marsairforce/nobsound/pictures/IMG_5804.jpg

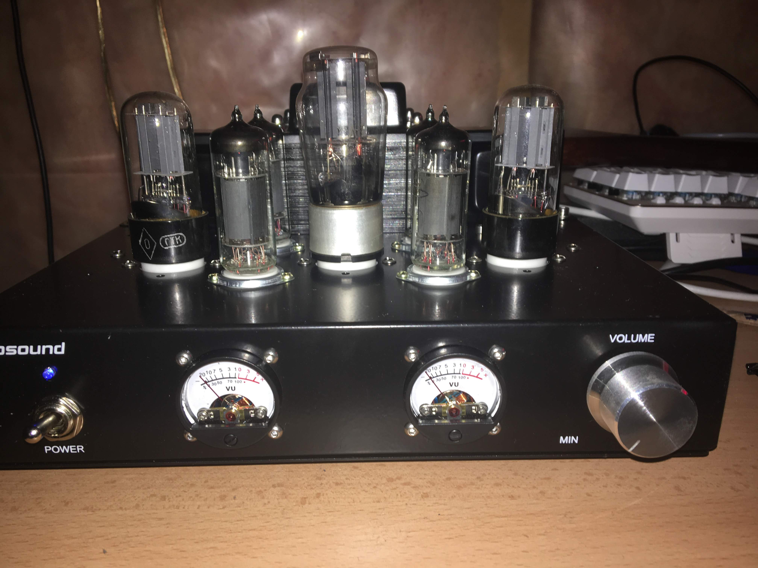
pictures/IMG_5804.jpg
