marsairforce/nobsound/pictures/IMG_5805.jpg

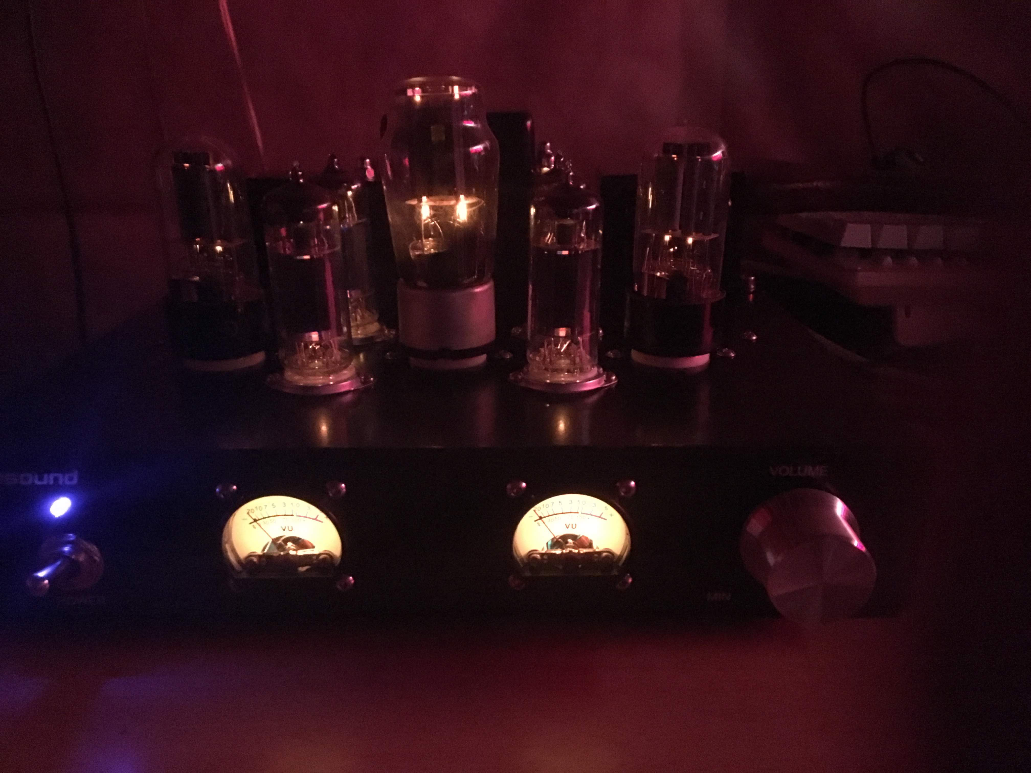
pictures/IMG_5805.jpg
