marsairforce/nobsound/pictures/IMG_9100.jpg

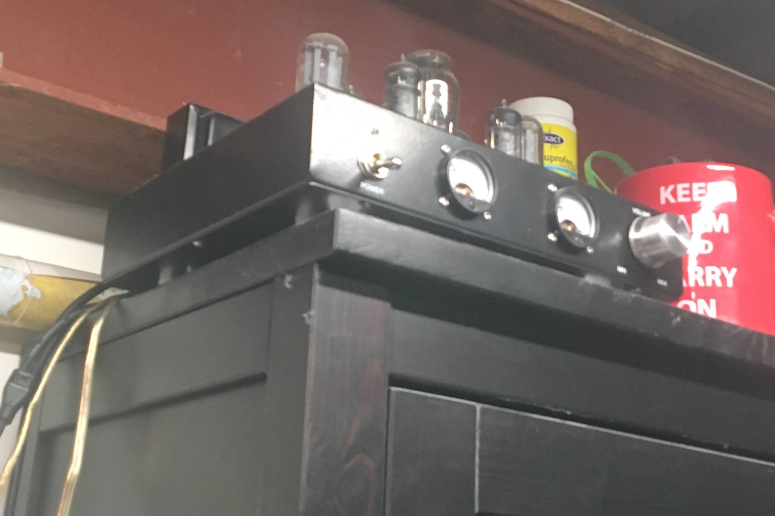
pictures/IMG_9100.jpg
