marsairforce/nobsound/pictures/IMG_9361(1).jpg

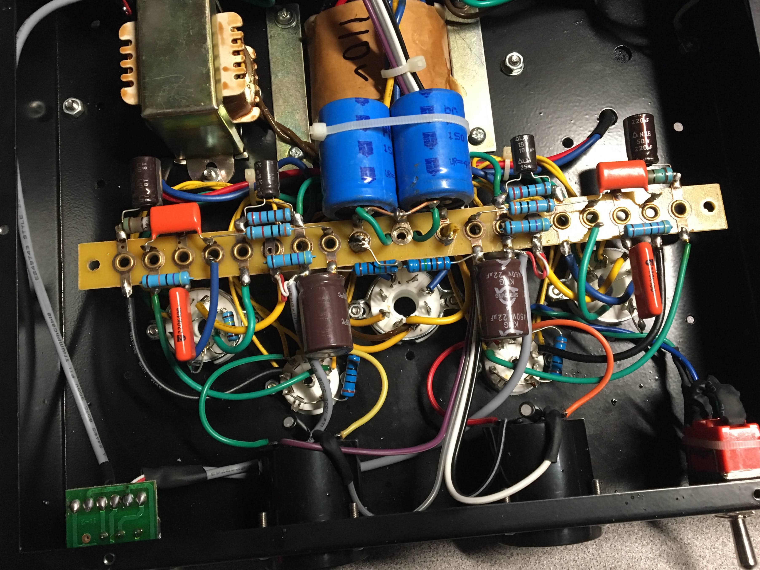
pictures/IMG_9361(1).jpg
