marsairforce/nobsound/pictures/IMG_9361.jpg

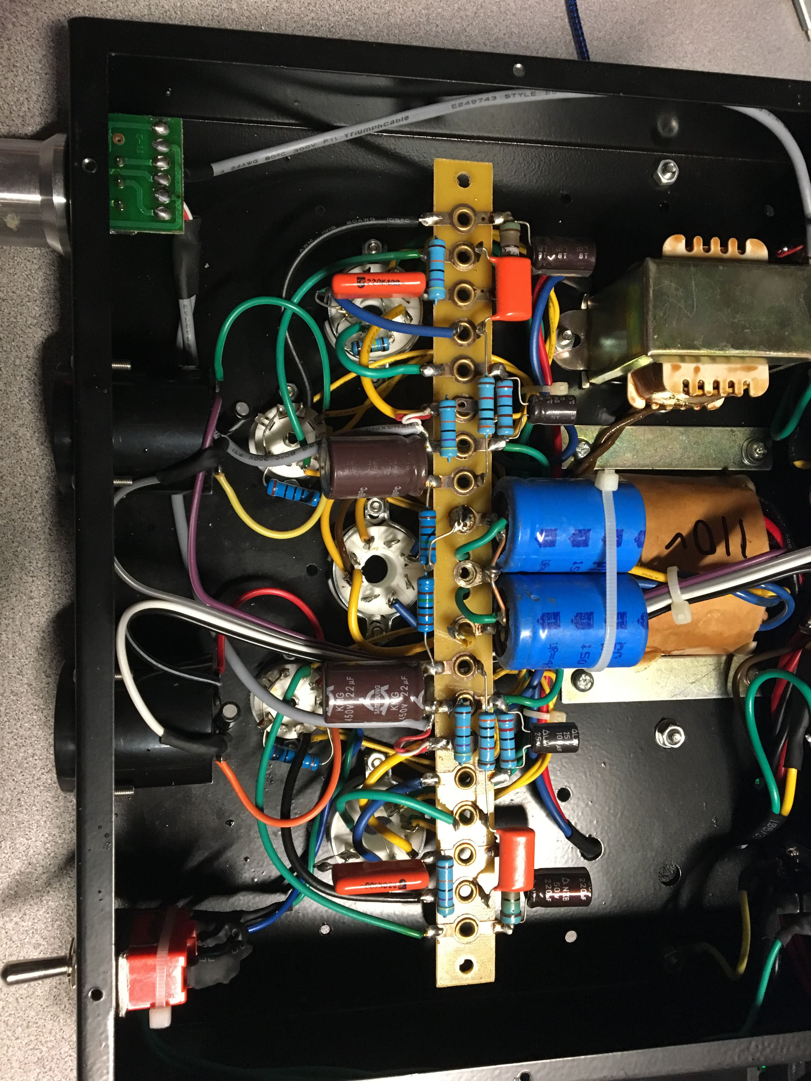
pictures/IMG_9361.jpg
