marsairforce/nobsound/pictures/IMG_9362.jpg

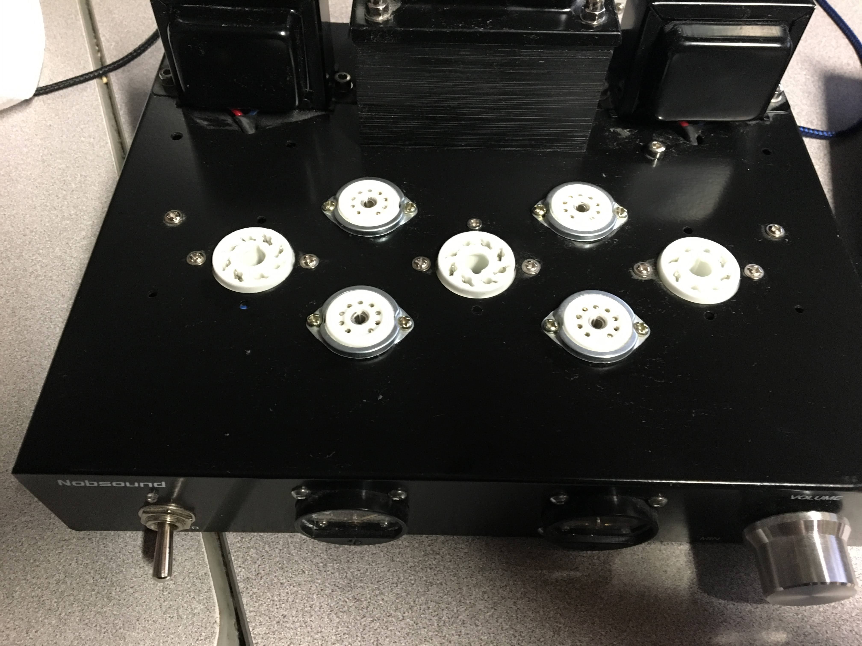
pictures/IMG_9362.jpg
