marsairforce/nobsound/pictures/IMG_9363.jpg

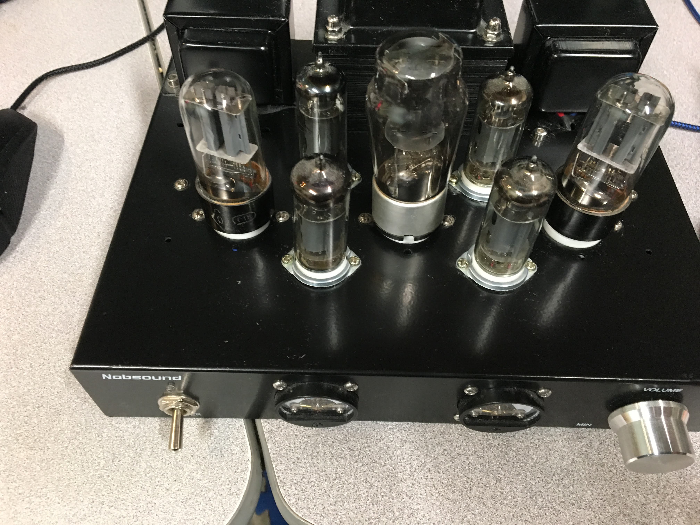
pictures/IMG_9363.jpg
