marsairforce/nobsound/pictures/IMG_9367.jpg

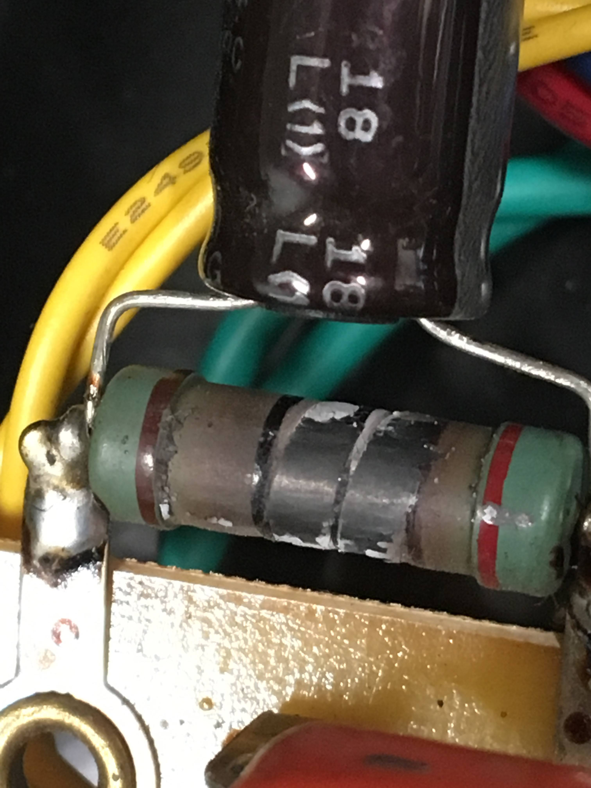
pictures/IMG_9367.jpg
