marsairforce/nobsound/pictures/IMG_9372.jpg

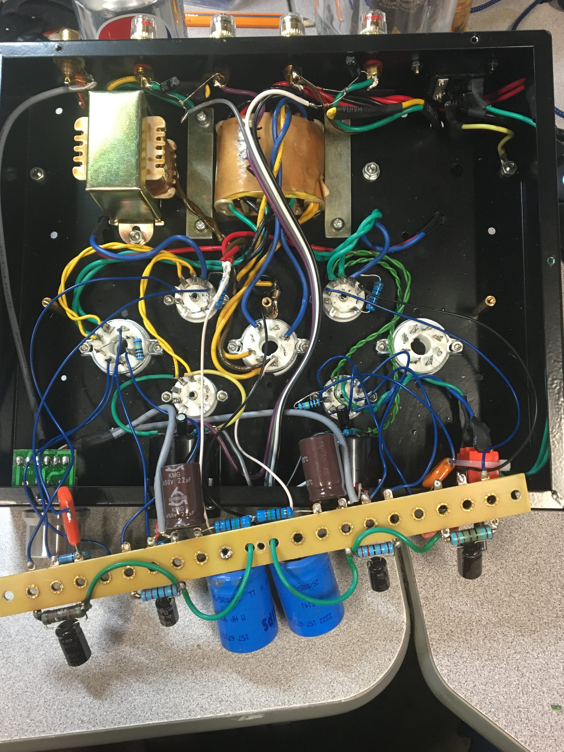
pictures/IMG_9372.jpg
