marsairforce/nobsound/pictures/IMG_9373.jpg

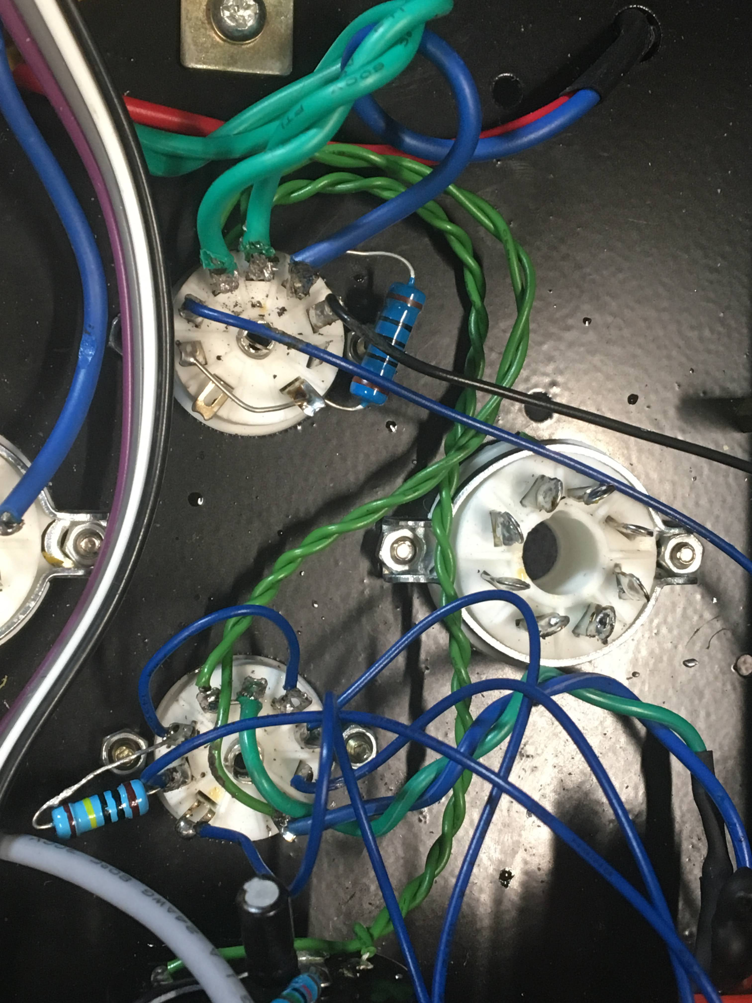
pictures/IMG_9373.jpg
