marsairforce/nobsound/pictures/IMG_9374.jpg

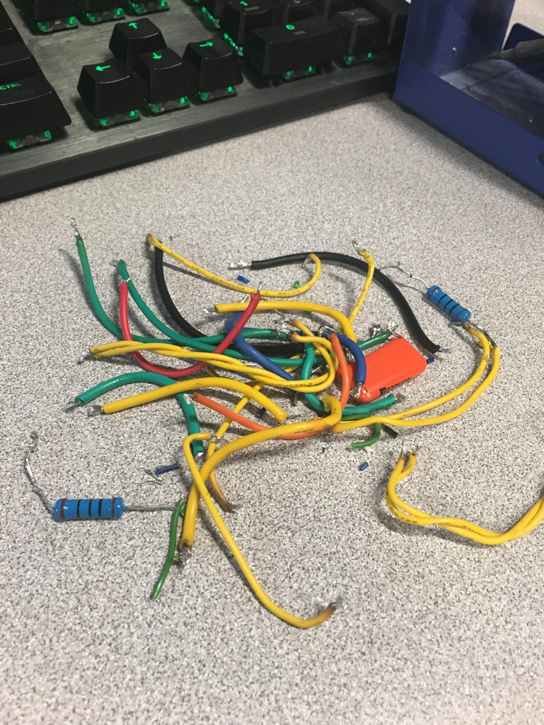
pictures/IMG_9374.jpg
