marsairforce/nobsound/pictures/IMG_9375.jpg

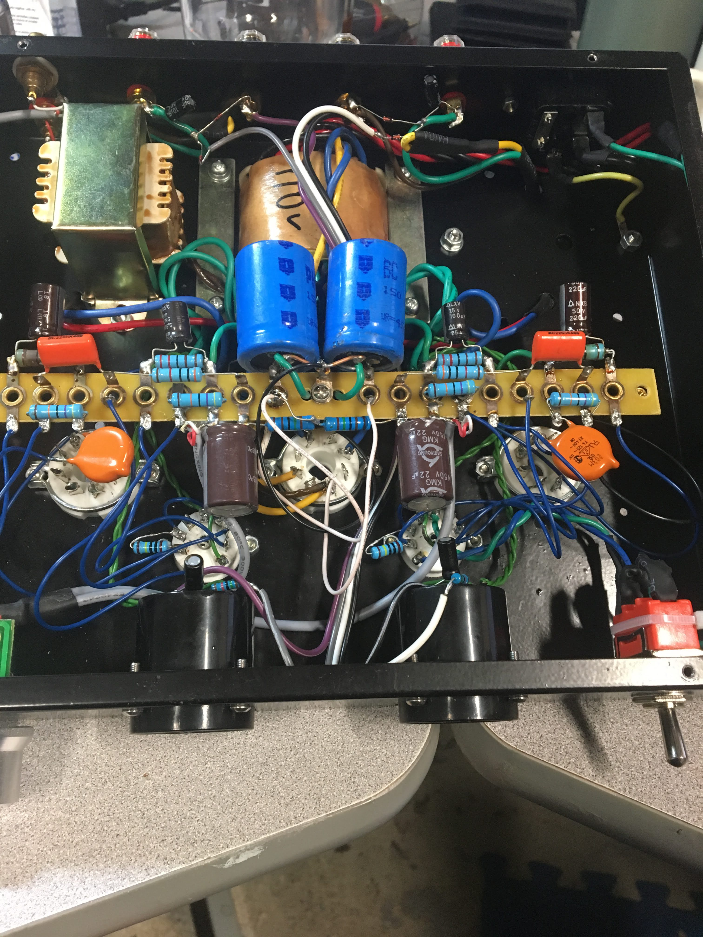
pictures/IMG_9375.jpg
