marsairforce/nobsound/pictures/IMG_9376.jpg

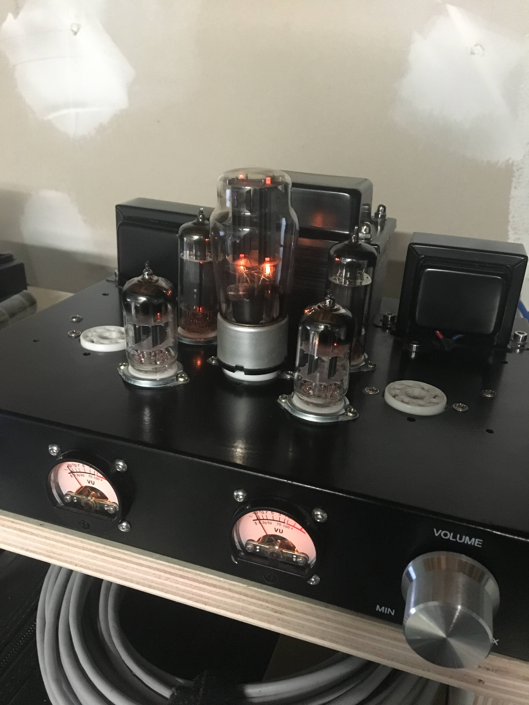
pictures/IMG_9376.jpg
