marsairforce/nobsound/pictures/IMG_9391.jpg

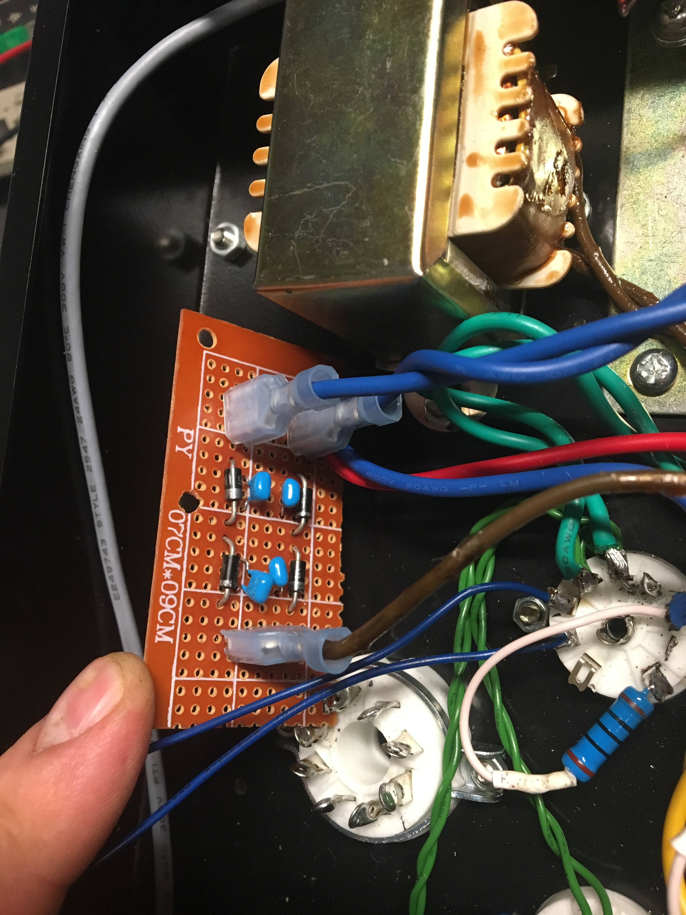
pictures/IMG_9391.jpg
