marsairforce/nobsound/pictures/IMG_9392.jpg

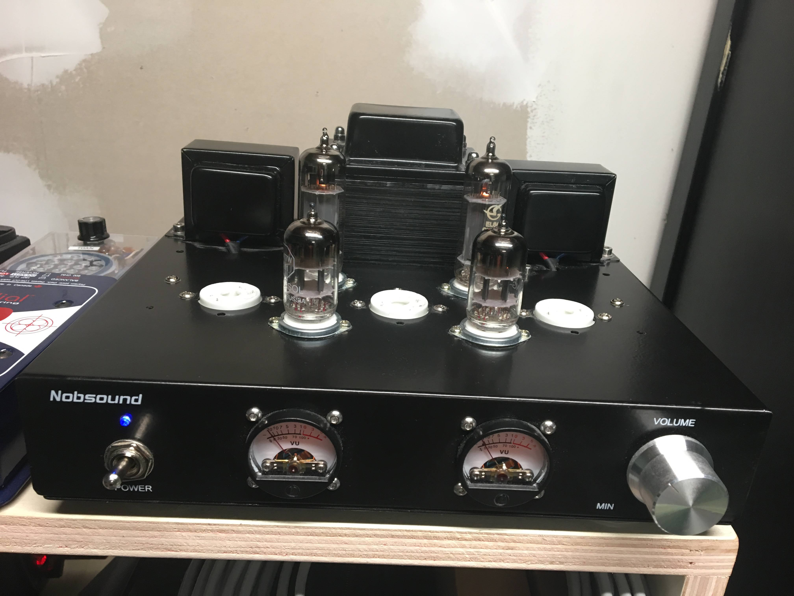
pictures/IMG_9392.jpg
