marsairforce/nobsound/pictures/IMG_9437.jpg

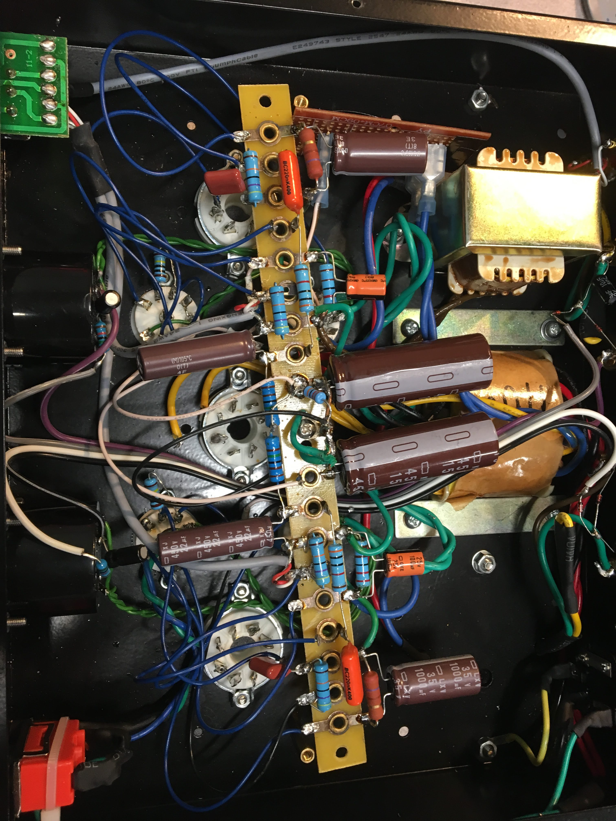
pictures/IMG_9437.jpg
