marsairforce/nobsound/pictures/IMG_9438.jpg

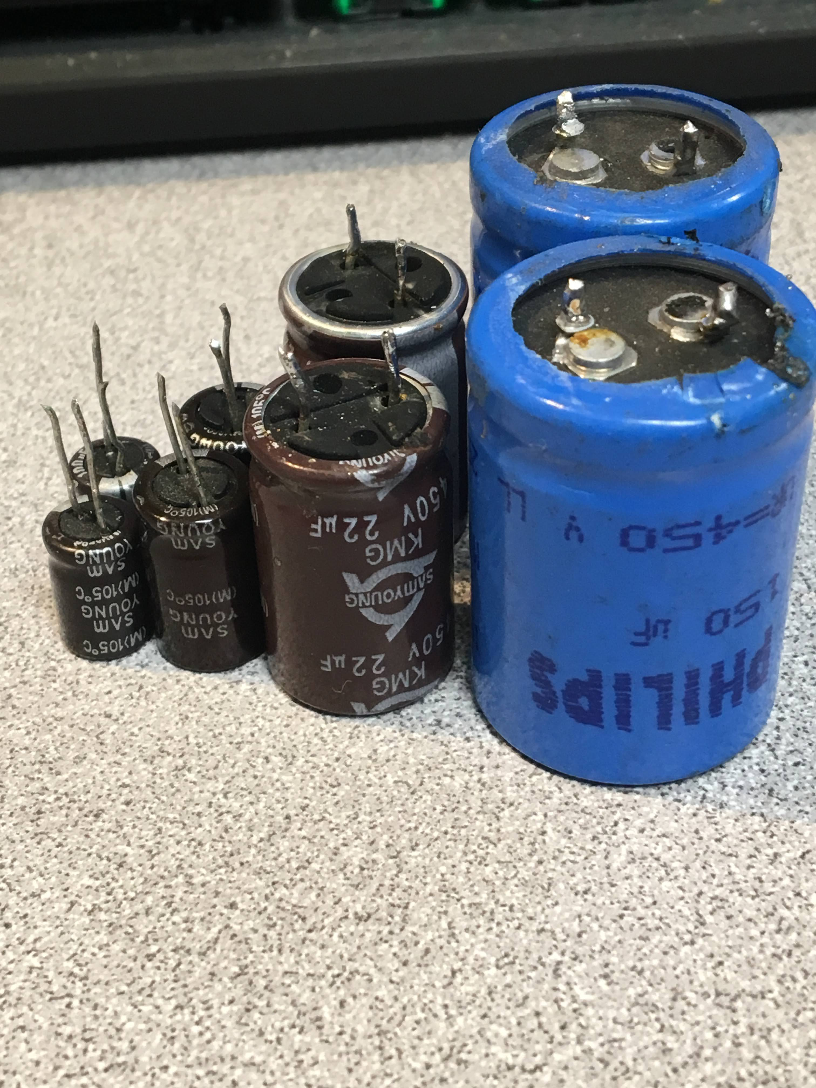
pictures/IMG_9438.jpg
