marsairforce/nobsound/pictures/IMG_9439.jpg

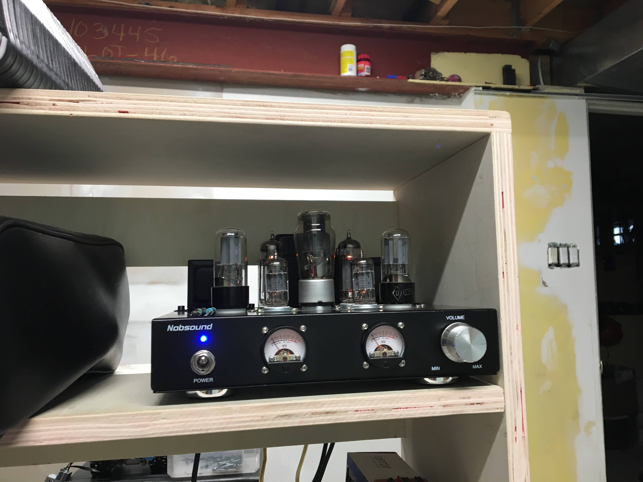
pictures/IMG_9439.jpg
