marsairforce/nobsound/pictures/IMG_9770.jpg

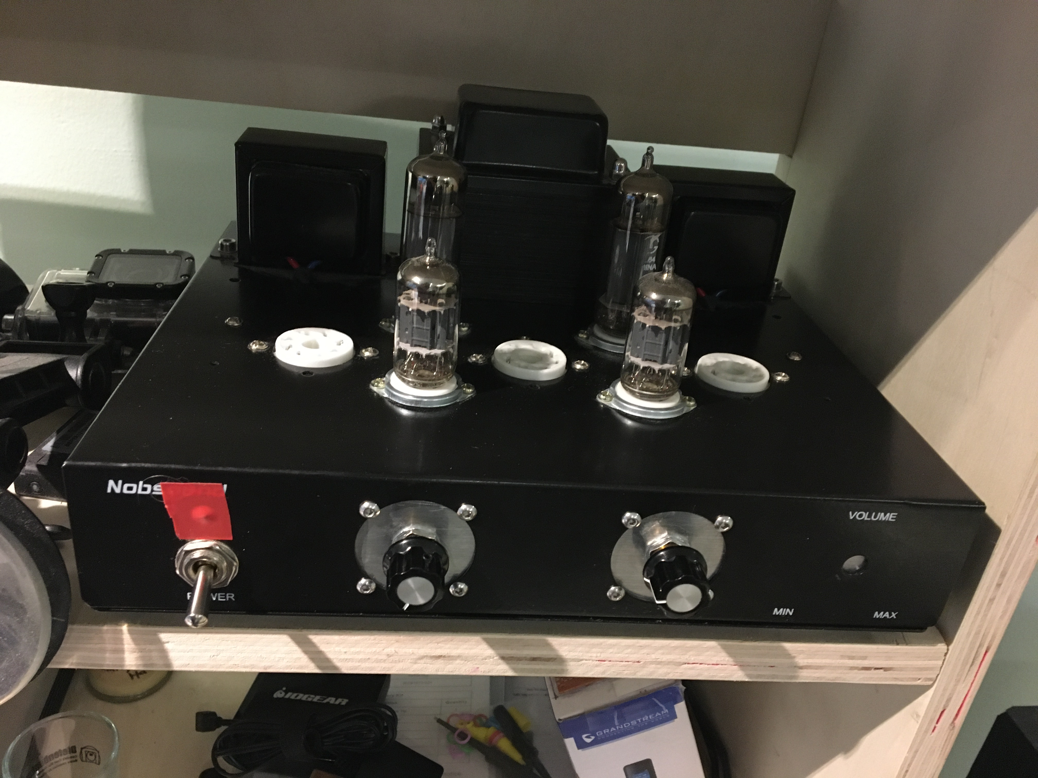
pictures/IMG_9770.jpg
