marsairforce/nobsound/pictures/IMG_9871.jpg

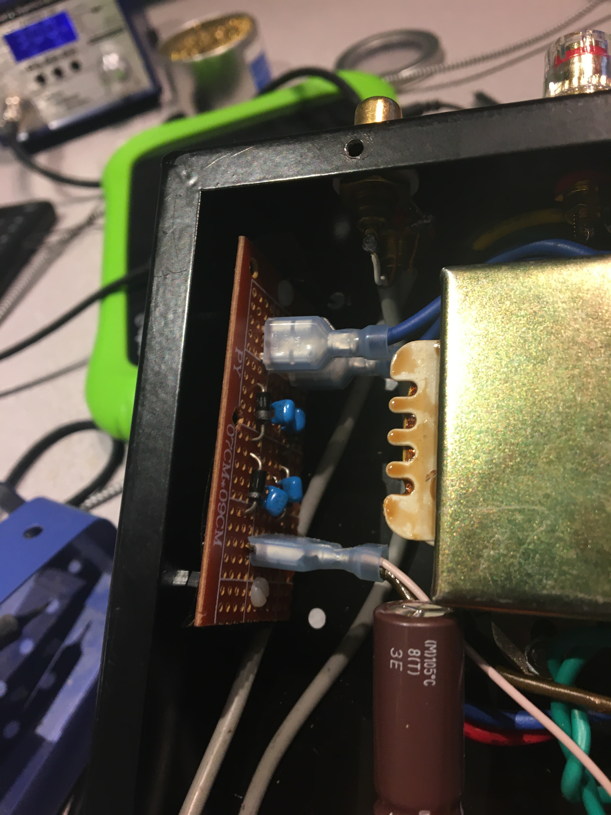
pictures/IMG_9871.jpg
