marsairforce/nobsound/pictures/IMG_9872.jpg

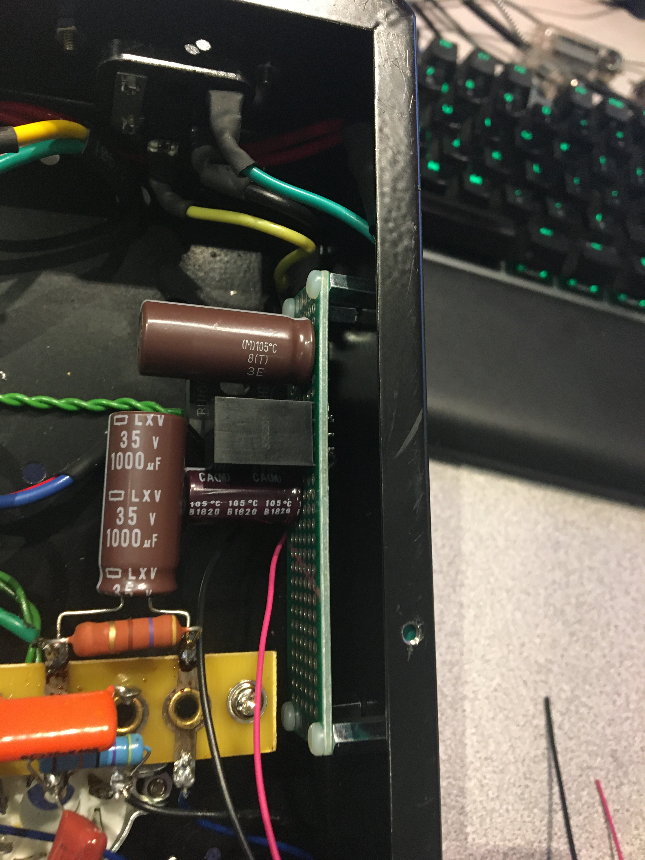
pictures/IMG_9872.jpg
