marsairforce/nobsound/pictures/IMG_9875.jpg

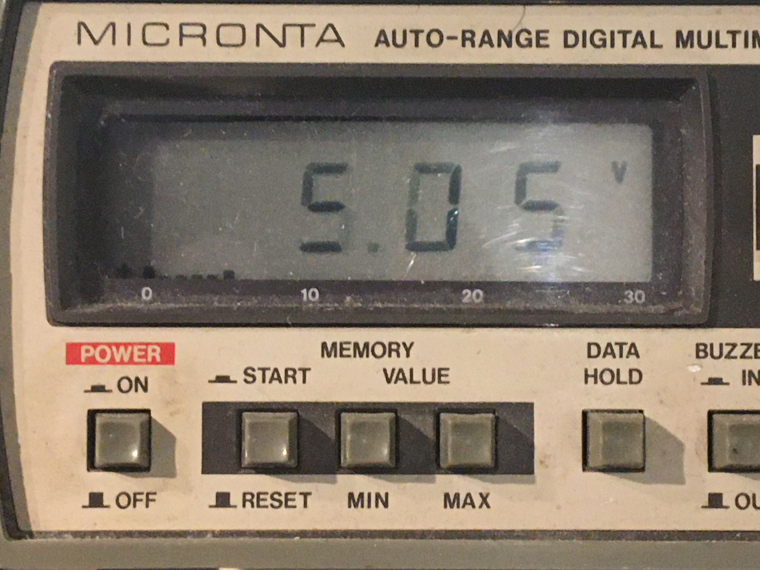
pictures/IMG_9875.jpg
