marsairforce/nobsound/pictures/IMG_9899.jpg

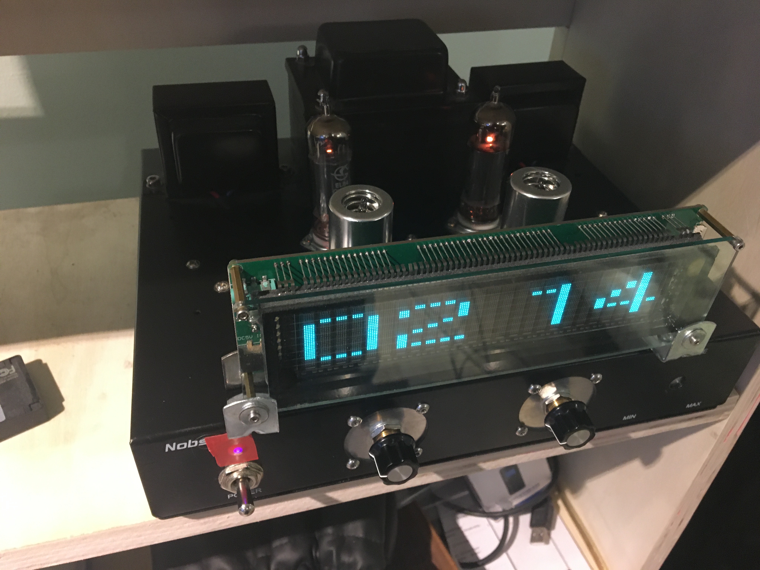
pictures/IMG_9899.jpg
