marsairforce/nobsound/pictures/IMG_9910.jpg

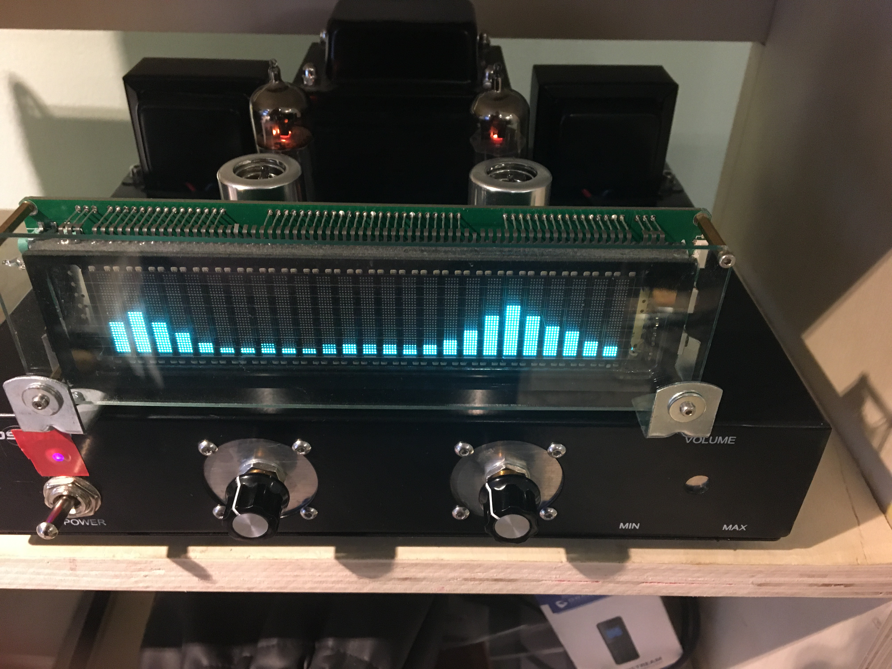
pictures/IMG_9910.jpg
