marsairforce/nobsound/updated/0355st-A.png

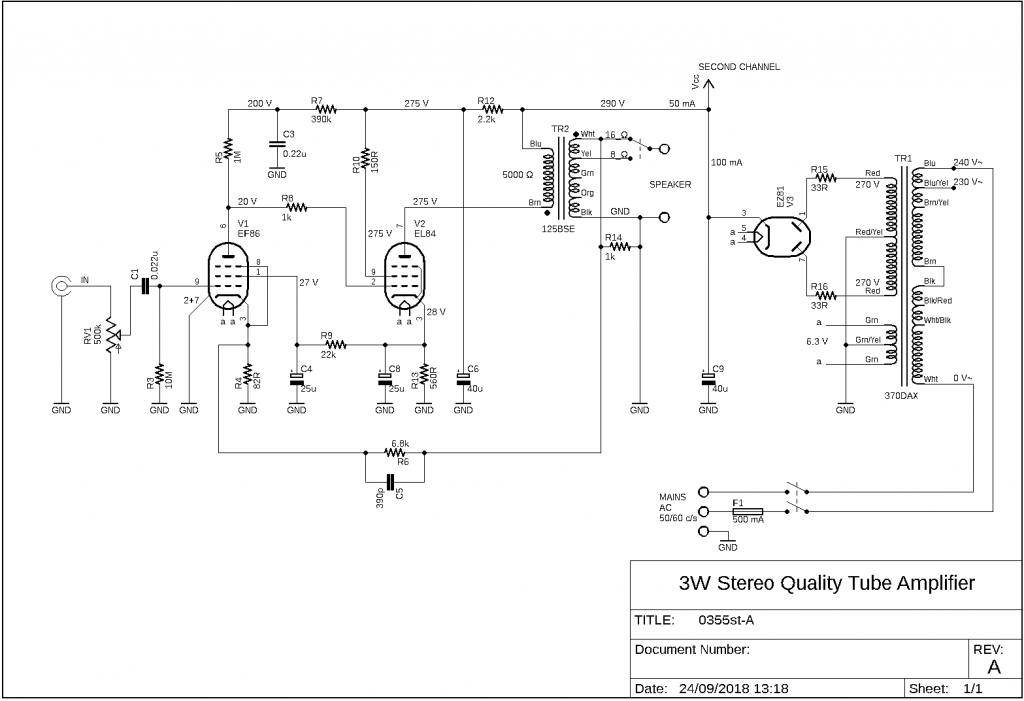
updated/0355st-A.png
