marsairforce/nobsound/updated/EF86 preamp.jpg

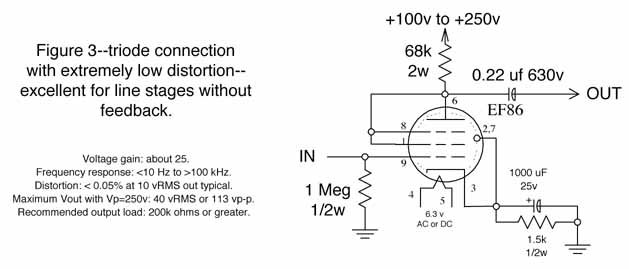
updated/EF86 preamp.jpg
