marsairforce/nobsound/pictures/IMG_9378.jpg

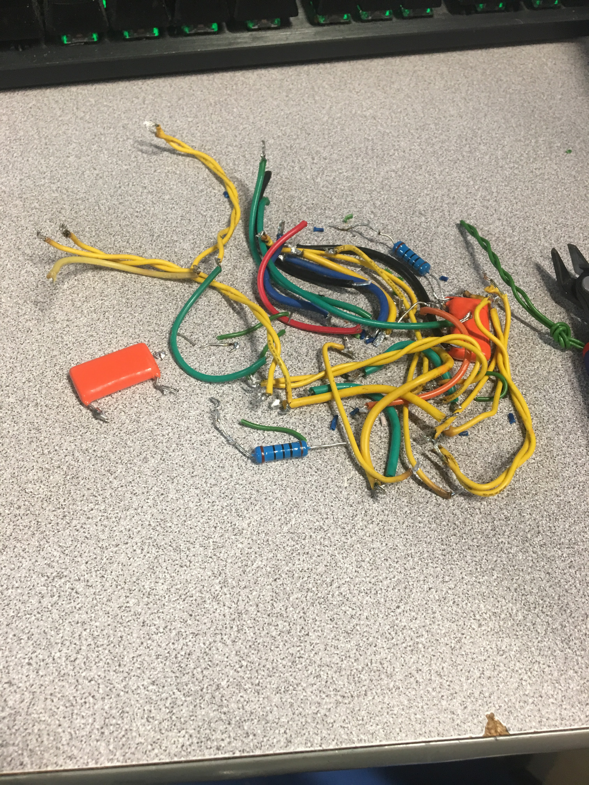
pictures/IMG_9378.jpg
