marsairforce/nobsound/pictures/IMG_9380.jpg

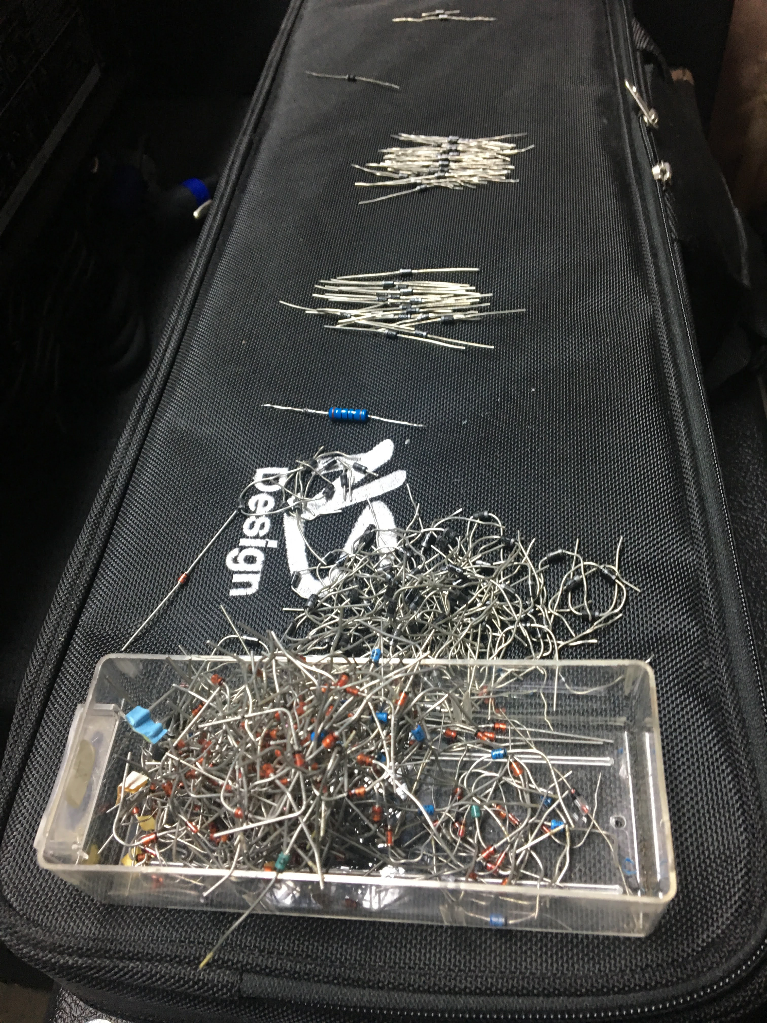
pictures/IMG_9380.jpg
