marsairforce/nobsound/pictures/IMG_9769.jpg

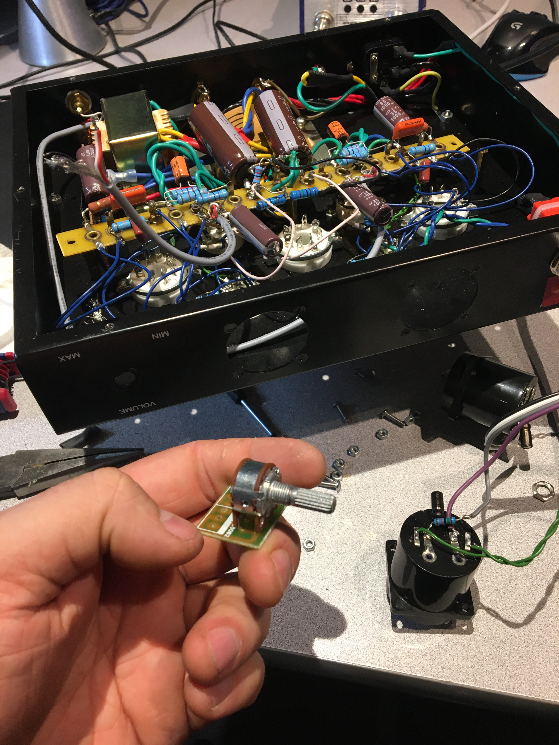
pictures/IMG_9769.jpg
