marsairforce/nobsound/pictures/IMG_9874.jpg

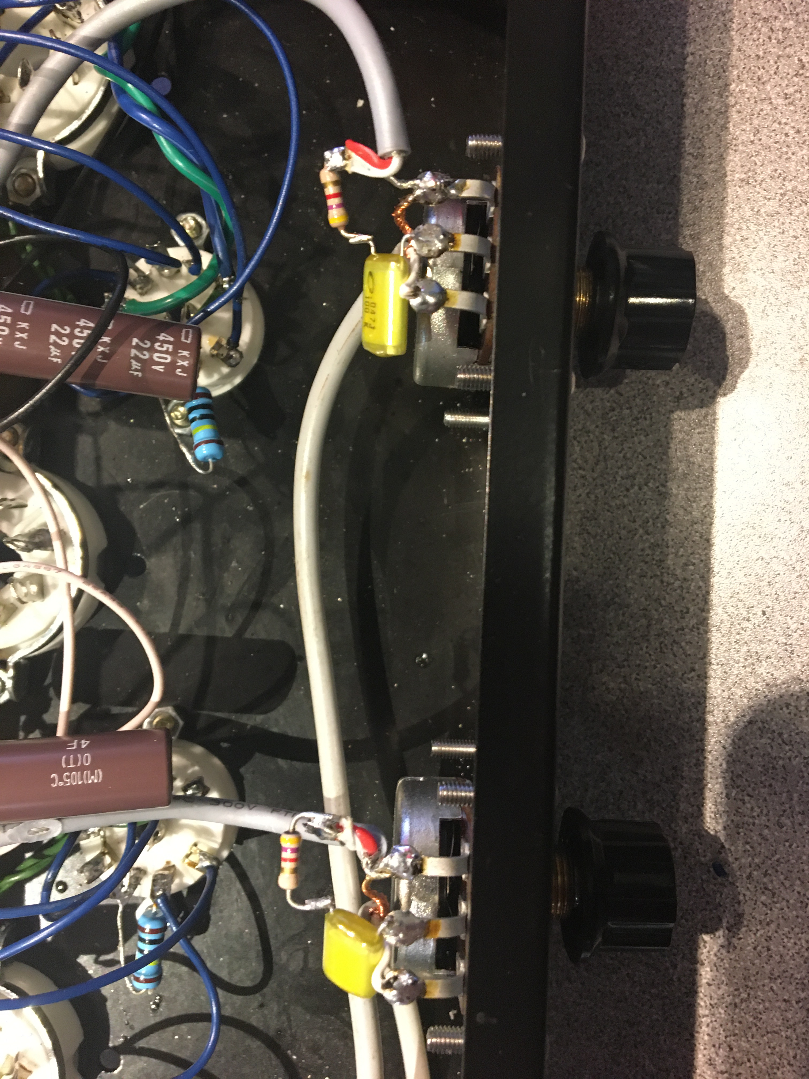
pictures/IMG_9874.jpg
